c-/AiLight-Flasher/Pictures/IMG_20190606_125135.jpg

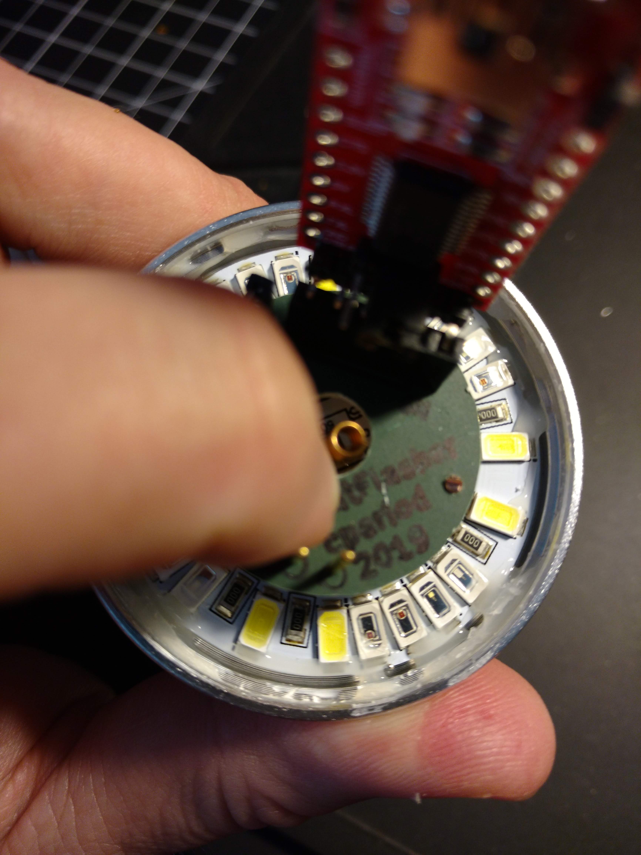
Pictures/IMG_20190606_125135.jpg
