c-/AiLight-Flasher/Pictures/IMG_20190811_100513.jpg

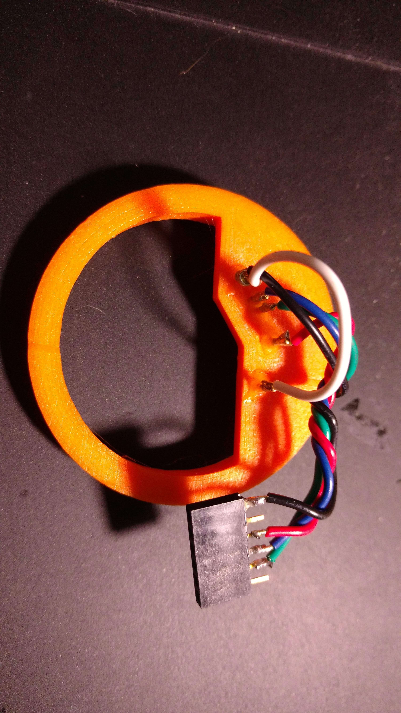
Pictures/IMG_20190811_100513.jpg
