c-/AiLight-Flasher/Pictures/IMG_20190811_100538.jpg

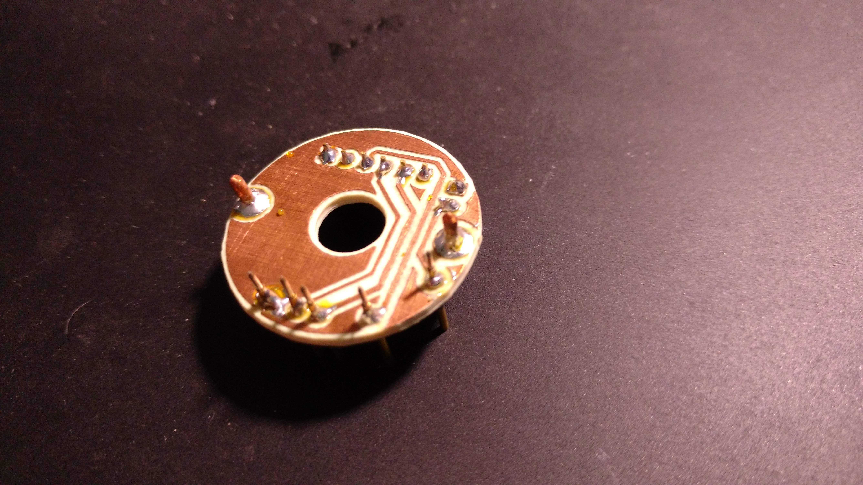
Pictures/IMG_20190811_100538.jpg
